xz-group/PCBench/trezor-one/src/images/IMG_1489.JPG

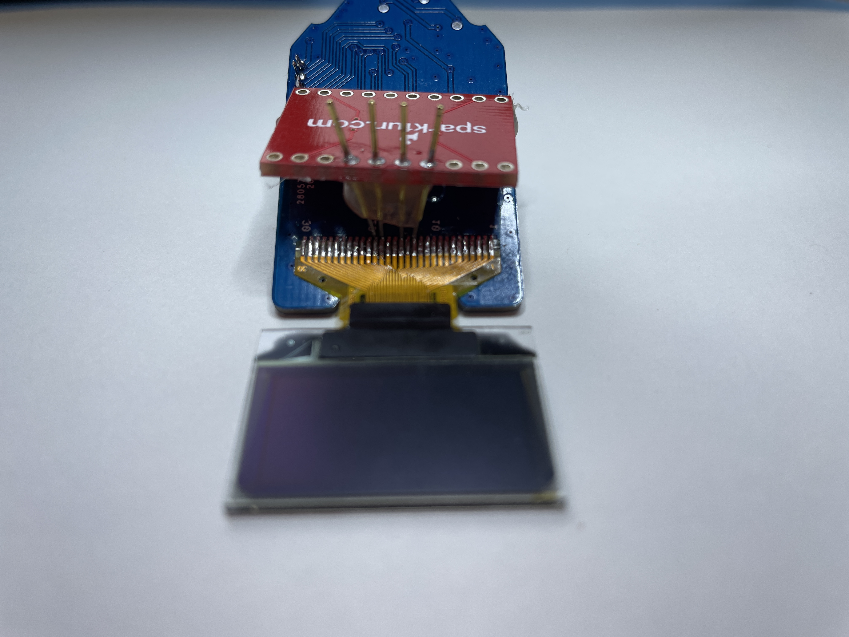
trezor-one/src/images/IMG_1489.JPG
