xz-group/PCBench/trezor-one/src/images/IMG_1491.JPG

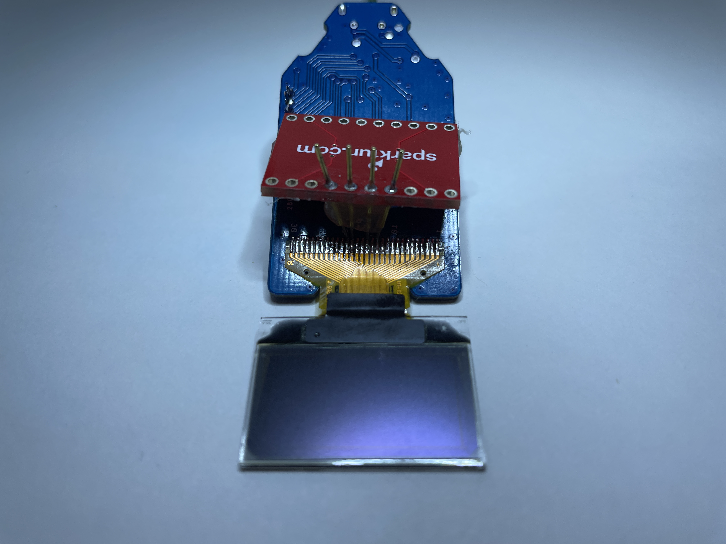
trezor-one/src/images/IMG_1491.JPG
