xz-group/PCBench/trezor-one/src/images/IMG_1494.JPG

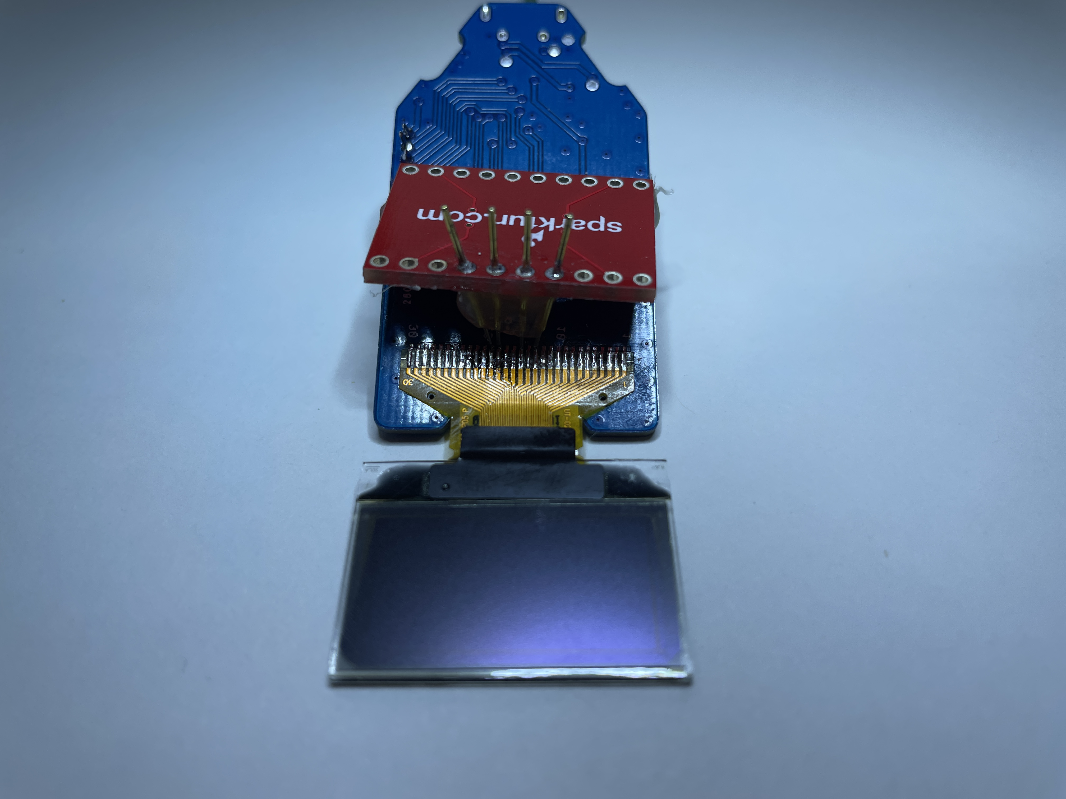
trezor-one/src/images/IMG_1494.JPG
