xz-group/PCBench/trezor-one/src/images/IMG_1496.JPG

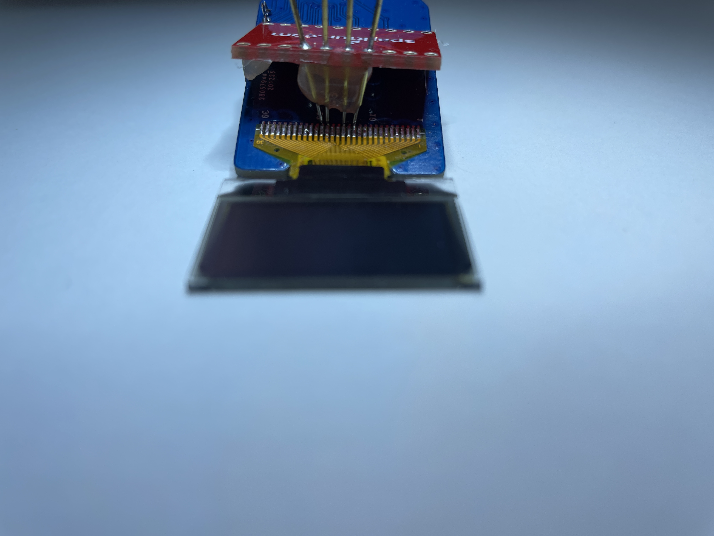
trezor-one/src/images/IMG_1496.JPG
