xz-group/PCBench/arduino-due/src/attiny102f_sw/erase_uart_/erase_uart_/include/atmel_start_pins.h

/*
 * Code generated from Atmel Start.
 *
 * This file will be overwritten when reconfiguring your Atmel Start project.
 * Please copy examples or other code you want to keep to a separate file
 * to avoid losing it when reconfiguring.
 */
#ifndef ATMEL_START_PINS_H_INCLUDED
#define ATMEL_START_PINS_H_INCLUDED

#include <port.h>

/**
 * \brief Set erase_payload pull mode
 *
 * Configure pin to pull up, down or disable pull mode, supported pull
 * modes are defined by device used
 *
 * \param[in] pull_mode Pin pull mode
 */
static inline void erase_payload_set_pull_mode(const enum port_pull_mode pull_mode)
{
	PORTA_set_pin_pull_mode(0, pull_mode);
}

/**
 * \brief Set erase_payload data direction
 *
 * Select if the pin data direction is input, output or disabled.
 * If disabled state is not possible, this function throws an assert.
 *
 * \param[in] direction PORT_DIR_IN  = Data direction in
 *                      PORT_DIR_OUT = Data direction out
 *                      PORT_DIR_OFF = Disables the pin
 *                      (low power state)
 */
static inline void erase_payload_set_dir(const enum port_dir dir)
{
	PORTA_set_pin_dir(0, dir);
}

/**
 * \brief Set erase_payload level
 *
 * Sets output level on a pin
 *
 * \param[in] level true  = Pin level set to "high" state
 *                  false = Pin level set to "low" state
 */
static inline void erase_payload_set_level(const bool level)
{
	PORTA_set_pin_level(0, level);
}

/**
 * \brief Toggle output level on erase_payload
 *
 * Toggle the pin level
 */
static inline void erase_payload_toggle_level()
{
	PORTA_toggle_pin_level(0);
}

/**
 * \brief Get level on erase_payload
 *
 * Reads the level on a pin
 */
static inline bool erase_payload_get_level()
{
	return PORTA_get_pin_level(0);
}

/**
 * \brief Set PB2 pull mode
 *
 * Configure pin to pull up, down or disable pull mode, supported pull
 * modes are defined by device used
 *
 * \param[in] pull_mode Pin pull mode
 */
static inline void PB2_set_pull_mode(const enum port_pull_mode pull_mode)
{
	PORTB_set_pin_pull_mode(2, pull_mode);
}

/**
 * \brief Set PB2 data direction
 *
 * Select if the pin data direction is input, output or disabled.
 * If disabled state is not possible, this function throws an assert.
 *
 * \param[in] direction PORT_DIR_IN  = Data direction in
 *                      PORT_DIR_OUT = Data direction out
 *                      PORT_DIR_OFF = Disables the pin
 *                      (low power state)
 */
static inline void PB2_set_dir(const enum port_dir dir)
{
	PORTB_set_pin_dir(2, dir);
}

/**
 * \brief Set PB2 level
 *
 * Sets output level on a pin
 *
 * \param[in] level true  = Pin level set to "high" state
 *                  false = Pin level set to "low" state
 */
static inline void PB2_set_level(const bool level)
{
	PORTB_set_pin_level(2, level);
}

/**
 * \brief Toggle output level on PB2
 *
 * Toggle the pin level
 */
static inline void PB2_toggle_level()
{
	PORTB_toggle_pin_level(2);
}

/**
 * \brief Get level on PB2
 *
 * Reads the level on a pin
 */
static inline bool PB2_get_level()
{
	return PORTB_get_pin_level(2);
}

/**
 * \brief Set PB3 pull mode
 *
 * Configure pin to pull up, down or disable pull mode, supported pull
 * modes are defined by device used
 *
 * \param[in] pull_mode Pin pull mode
 */
static inline void PB3_set_pull_mode(const enum port_pull_mode pull_mode)
{
	PORTB_set_pin_pull_mode(3, pull_mode);
}

/**
 * \brief Set PB3 data direction
 *
 * Select if the pin data direction is input, output or disabled.
 * If disabled state is not possible, this function throws an assert.
 *
 * \param[in] direction PORT_DIR_IN  = Data direction in
 *                      PORT_DIR_OUT = Data direction out
 *                      PORT_DIR_OFF = Disables the pin
 *                      (low power state)
 */
static inline void PB3_set_dir(const enum port_dir dir)
{
	PORTB_set_pin_dir(3, dir);
}

/**
 * \brief Set PB3 level
 *
 * Sets output level on a pin
 *
 * \param[in] level true  = Pin level set to "high" state
 *                  false = Pin level set to "low" state
 */
static inline void PB3_set_level(const bool level)
{
	PORTB_set_pin_level(3, level);
}

/**
 * \brief Toggle output level on PB3
 *
 * Toggle the pin level
 */
static inline void PB3_toggle_level()
{
	PORTB_toggle_pin_level(3);
}

/**
 * \brief Get level on PB3
 *
 * Reads the level on a pin
 */
static inline bool PB3_get_level()
{
	return PORTB_get_pin_level(3);
}

#endif /* ATMEL_START_PINS_H_INCLUDED */
