xz-group/PCBench/trezor-one/src/SPI_Manual_Test/SPI_Manual_Test.ino

#include <SPI.h>
#include <Wire.h>

#define SS 2
#define DC 3
#define RST 4

byte startup[] = {0xAE, 0xD5, 0x80, 0xA8, 0x3F, 0xD3, 0x00, 0x40, 0x8D, 0x14, 0x20, 0x00, 0xA1, 0xC8, 0xDA, 0x12, 0x81, 0xCF, 0xD9, 0xF1, 0xDB, 0x40, 0xA4, 0xA6, 0xAF};
byte preData[] = {0x00, 0x10, 0x40};
void setup() {
  pinMode(SS, OUTPUT);
  pinMode(DC, OUTPUT);
  pinMode(RST, OUTPUT);
  digitalWrite(SS, HIGH);  // ensure SS stays high
  digitalWrite(DC, LOW);  // start data/control low (control mode)
  digitalWrite(RST, HIGH);
  
  SPI.setBitOrder(MSBFIRST);
  SPI.setClockDivider(SPI_CLOCK_DIV8);
  SPI.setDataMode(0);
  SPI.begin();
  
  Serial.begin(9600);
  delay(100);

  digitalWrite(RST, HIGH);
  delay(1);
  digitalWrite(RST, LOW);
  delay(10);
  digitalWrite(RST, HIGH);

  //startup
  digitalWrite(SS, HIGH);
  digitalWrite(DC, LOW);
  digitalWrite(SS, LOW); 
  for(int i=0; i < sizeof(startup)/sizeof(byte); i++) {
      //Serial.println(startup[i]);
      SPI.transfer(startup[i]);
  }
  digitalWrite(SS, HIGH);

  digitalWrite(SS, LOW); 
  for(int i=0; i < sizeof(preData)/sizeof(byte); i++) {
      SPI.transfer(preData[i]);
  }
  digitalWrite(SS, HIGH);

  //start blank
  digitalWrite(SS, LOW); 
  digitalWrite(DC, HIGH);
  for(int i=0; i < 1024; i++) {
    SPI.transfer(0x00);
  }
  digitalWrite(DC, LOW);
  digitalWrite(SS, HIGH); 


  digitalWrite(SS, LOW); 
  for(int i=0; i < sizeof(preData)/sizeof(byte); i++) {
      SPI.transfer(preData[i]);
  }
  digitalWrite(SS, HIGH);

  //pixel data
  digitalWrite(SS, LOW); 
  digitalWrite(DC, HIGH);



SPI.transfer(0x00);
SPI.transfer(0x00);
SPI.transfer(0x00);
SPI.transfer(0x00);
SPI.transfer(0x00);
SPI.transfer(0x00);
SPI.transfer(0x00);
SPI.transfer(0x00);
SPI.transfer(0x00);
SPI.transfer(0x00);
SPI.transfer(0x00);
SPI.transfer(0x00);
SPI.transfer(0x00);
SPI.transfer(0x00);
SPI.transfer(0x00);
SPI.transfer(0x00);
SPI.transfer(0x00);
SPI.transfer(0x00);
SPI.transfer(0x00);
SPI.transfer(0x00);
SPI.transfer(0x00);
SPI.transfer(0x00);
SPI.transfer(0x00);
SPI.transfer(0x00);
SPI.transfer(0x00);
SPI.transfer(0x00);
SPI.transfer(0x00);
SPI.transfer(0x00);
SPI.transfer(0x00);
SPI.transfer(0x00);
SPI.transfer(0x00);
SPI.transfer(0x00);
SPI.transfer(0x00);
SPI.transfer(0x00);
SPI.transfer(0x00);
SPI.transfer(0x00);
SPI.transfer(0x00);
SPI.transfer(0x00);
SPI.transfer(0x00);
SPI.transfer(0x00);
SPI.transfer(0x00);
SPI.transfer(0x00);
SPI.transfer(0x00);
SPI.transfer(0x00);
SPI.transfer(0x00);
SPI.transfer(0x00);
SPI.transfer(0x00);
SPI.transfer(0x00);
SPI.transfer(0x00);
SPI.transfer(0x00);
SPI.transfer(0x00);
SPI.transfer(0x00);
SPI.transfer(0x00);
SPI.transfer(0x00);
SPI.transfer(0x00);
SPI.transfer(0x00);
SPI.transfer(0x00);
SPI.transfer(0x00);
SPI.transfer(0x00);
SPI.transfer(0x00);
SPI.transfer(0x00);
SPI.transfer(0x00);
SPI.transfer(0x00);
SPI.transfer(0x00);
SPI.transfer(0x00);
SPI.transfer(0x00);
SPI.transfer(0x00);
SPI.transfer(0x00);
SPI.transfer(0x00);
SPI.transfer(0x00);
SPI.transfer(0x00);
SPI.transfer(0x00);
SPI.transfer(0x00);
SPI.transfer(0x00);
SPI.transfer(0x00);
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
SPI.transfer(0xF8);
SPI.transfer(0xFC);
SPI.transfer(0xFC);
SPI.transfer(0xF8);
SPI.transfer(0xF1);
SPI.transfer(0x7B);
SPI.transfer(0x3F);
SPI.transfer(0x1F);
SPI.transfer(0x0F);
SPI.transfer(0x07);



  digitalWrite(DC, LOW);
  digitalWrite(SS, HIGH); 
}

void loop() {

  

  

}
